donnersm/FFT_ESP32_Analyzer/Main Sketch/V1.0/FFT.h

 /********************************************************************************************************************************************************
 *                                                                                                                                                       *
 *  Project:         FFT Spectrum Analyzer                                                                                                               *
 *  Target Platform: ESP32                                                                                                                               *
 *                                                                                                                                                       * 
 *  Version: 1.0                                                                                                                                         *
 *  Hardware setup: See github                                                                                                                           *
 *  Spectrum analyses done with analog chips MSGEQ7                                                                                                      *
 *                                                                                                                                                       * 
 *  Mark Donners                                                                                                                                         *
 *  The Electronic Engineer                                                                                                                              *
 *  Website:   www.theelectronicengineer.nl                                                                                                              *
 *  facebook:  https://www.facebook.com/TheelectronicEngineer                                                                                            *
 *  youtube:   https://www.youtube.com/channel/UCm5wy-2RoXGjG2F9wpDFF3w                                                                                  *
 *  github:    https://github.com/donnersm                                                                                                               *
 *                                                                                                                                                       *  
 ********************************************************************************************************************************************************/
 
#pragma once
// Depending on how many bands have been defined, one of these tables will contain the frequency
// cutoffs for that "size" of a spectrum display. 
// Only one of the following should be 1, rest has to be 0 
// WARNING amke sure your math add up.. if you select 24 bands on a 32 wide matrix....you'll need to adjust code 
#define bands8  0
#define bands16 0
#define bands24 0
#define bands32 1
#define bands64 0  
int CalibrationType=0;  //0=none, 1=White, 2=Pink     
char Filtername[4][6]={
  "None",  // see documentation on this one.
  "Pink",
  "White",
  "Brown"
};
#if bands8
const int numBands = 8;
  static int BandCutoffTable[8] =
  {
   20, 150, 400, 550, 675, 780, 900, 1200
  };

  static double BandCalibration_Pink[8]=
  { 4.08, 1.56, 1.00, 2.80, 3.23, 3.63, 6.19, 1.65 };
  static double BandCalibration_White[8]=
  { 25.84, 3.43, 1.10, 2.95, 3.37, 3.39, 5.46, 1.00 };
  static double BandCalibration_Brown[8]=
  { 2.72, 1.17, 1.00, 3.34, 4.83, 5.57, 11.18, 3.08 };
#endif

#if bands16
  const int numBands = 16;
  static int BandCutoffTable[16] =
  {
   40, 60, 100, 150, 250, 400, 650, 1000, 1600, 2500, 4000, 6250, 12000, 14000, 16000, 17000
  };

  static double BandCalibration_Pink[16]=
{ 4.52, 5.48, 5.54, 6.06, 2.98, 1.72, 1.49, 1.36, 1.00, 1.49, 2.04, 1.71, 2.19, 2.68, 1.85, 5.69 };

  static double BandCalibration_White[16]=
{ 169.55, 148.58, 141.29, 124.24, 35.59, 10.76, 6.97, 5.18, 2.89, 4.19, 4.24, 1.99, 1.00, 1.60, 1.53, 5.48 }; 
    static double BandCalibration_Brown[16]=
{ 1.81, 2.17, 2.49, 2.89, 1.57, 1.00, 1.10, 1.30, 1.22, 3.74, 113.96, 774.90, 7.76, 645.75, 2583.00, 7749.00 };

#endif

#if bands24
  const int numBands = 24;
  static int BandCutoffTable[24] =
  {
    40, 80, 150, 220, 270, 320, 380, 440, 540, 630,  800, 1000, 1250, 1600, 2000, 2500, 3150, 
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
   48.56, 59.02, 67.90, 69.13, 71.71, 80.77, 91.35, 123.76, 134.61, 130.05, 18.44, 57.26, 62.38, 274.04, 426.28, 767.30, 1918.25, 306.92, 2557.67, 2557.67, 3836.50, 3000, 3000, 3836.50, 3000, 3000, 
   85.26, 3000, 3000, 99.65, 3000, 11.84, 13.46, 142.09, 2557.67, 7673.00, 2557.67 };

#endif
