donnersm/FFT_ESP32_Analyzer/Main Sketch/V1.0/logos.h

 /********************************************************************************************************************************************************
 *                                                                                                                                                       *
 *  Project:         FFT Spectrum Analyzer                                                                                                               *
 *  Target Platform: ESP32                                                                                                                               *
 *                                                                                                                                                       * 
 *  Version: 1.0                                                                                                                                         *
 *  Hardware setup: See github                                                                                                                           *
 *  Spectrum analyses done with analog chips MSGEQ7                                                                                                      *
 *                                                                                                                                                       * 
 *  Mark Donners                                                                                                                                         *
 *  The Electronic Engineer                                                                                                                              *
 *  Website:   www.theelectronicengineer.nl                                                                                                              *
 *  facebook:  https://www.facebook.com/TheelectronicEngineer                                                                                            *
 *  youtube:   https://www.youtube.com/channel/UCm5wy-2RoXGjG2F9wpDFF3w                                                                                  *
 *  github:    https://github.com/donnersm                                                                                                               *
 *                                                                                                                                                       *  
 ********************************************************************************************************************************************************/
 

//This file is only to display the logo, If you don't like the logo comment out:  drawLogo(); around line 81 in the main sketch
//You can also change it. It's a jpg converted to RGB 46x50px
// Image Size     : 46x50 pixels
// Memory usage   : 4600 bytes


#if defined(__AVR__)
    #include <avr/pgmspace.h>
#elif defined(__PIC32MX__)
    #define PROGMEM
#elif defined(__arm__)
    #define PROGMEM
#endif


// 'logo RGB', 46x50px
const unsigned long logo [] PROGMEM = {
  0x00000000, 0x00000000, 0x00000000, 0x00000000, 0x00000000, 0x00000000, 0x00000000, 0x00000000, 0x00000000, 0x00000000, 0x00000000, 0x00000000, 0x00000000, 0x00000000, 0x00000000, 0x00000000, 0x00000000, 0x00000000, 0x00000000, 0x00ffd42a, 0x00000000, 0x00000000, 0x00000000, 0x00000000, 0x00ffae0e, 0x00faad09, 0x00000000, 0x00000000, 0x00000000, 0x00000000, 0x00000000, 0x00000000, 0x00000000, 0x00000000, 0x00000000, 0x00000000, 0x00000000, 0x00000000, 0x00000000, 0x00000000, 0x00000000, 0x00000000, 0x00000000, 0x00000000, 0x00000000, 0x00000000, 
  0x00000000, 0x00000000, 0x00000000, 0x00000000, 0x00000000, 0x00000000, 0x00000000, 0x00000000, 0x00000000, 0x00000000, 0x00000000, 0x00000000, 0x00000000, 0x00000000, 0x00000000, 0x00000000, 0x00000000, 0x00000000, 0x00000000, 0x00fbac0a, 0x00faa708, 0x00000000, 0x00000000, 0x00000000, 0x00faab0a, 0x00faa908, 0x00000000, 0x00000000, 0x00000000, 0x00fba607, 0x00faaa08, 0x00000000, 0x00000000, 0x00000000, 0x00000000, 0x00000000, 0x00000000, 0x00000000, 0x00000000, 0x00000000, 0x00000000, 0x00000000, 0x00000000, 0x00000000, 0x00000000, 0x00000000, 
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
};

// Array of all bitmaps for convenience. (Total bytes used to store images in PROGMEM = 816)
const int epd_bitmap_allArray_LEN = 1;
const unsigned long* epd_bitmap_allArray[1] = {
  logo
};
